protospork/rack_parts/STL/rearpanel - 5U vertical opposite fan side bottom.stl

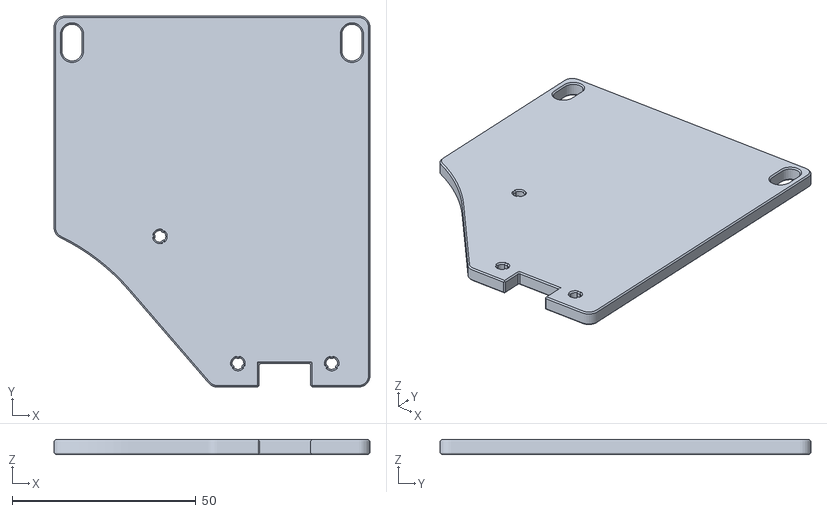
[picture p20: CAD file, 2025-03-12]
STL/rearpanel - 5U vertical opposite fan side bottom.stl
86.0 x 101.0 x 4.00
